weicocogoat/FYP_Integrate_MRAM-FPGA/FYP_Report/Chapter 4/ip-cores-communication_controller_i2c_slave/rtl/i2cSlave.v

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
`include "i2cSlave_define.v"


module i2cSlave (
  clk,
  rst,
  sda,
  scl,
  myReg0,
  myReg1,
  myReg2,
  myReg3,
  data_lb,
  data_ub,
  myReg6,
  myReg7,
  myReg8,
  myReg9,
  myReg10,
  myReg11,
  myReg12,
  myReg13,
  myReg14,
  myReg15,
  chip_en,
  read_en,
  write_en,
  lb_en,
  ub_en
);

input clk;
input rst;
inout sda;
input scl;
output [7:0] myReg0;
output [7:0] myReg1;
output [7:0] myReg2;
output [7:0] myReg3;
inout [7:0] data_lb;
inout [7:0] data_ub;
output [7:0] myReg6;
output [7:0] myReg7;
input [7:0] myReg8;
input [7:0] myReg9;
input [7:0] myReg10;
input [7:0] myReg11;
input [7:0] myReg12;
input [7:0] myReg13;
input [7:0] myReg14;
input [7:0] myReg15;
output chip_en;
output read_en;
output write_en;
output lb_en;
output ub_en;


// local wires and regs
reg sdaDeb;
reg sclDeb;
reg [`DEB_I2C_LEN-1:0] sdaPipe;
reg [`DEB_I2C_LEN-1:0] sclPipe;

reg [`SCL_DEL_LEN-1:0] sclDelayed;
reg [`SDA_DEL_LEN-1:0] sdaDelayed;
reg [1:0] startStopDetState;
wire clearStartStopDet;
wire sdaOut;
wire sdaIn;
wire [7:0] regAddr;
wire [7:0] dataToRegIF;
wire writeEn;
wire [7:0] dataFromRegIF;
reg [1:0] rstPipe;
wire rstSyncToClk;
reg startEdgeDet;

assign sda = (sdaOut == 1'b0) ? 1'b0 : 1'bz;
assign sdaIn = sda;

// sync rst rsing edge to clk
always @(posedge clk) begin
  if (rst == 1'b1)
    rstPipe <= 2'b11;
  else
    rstPipe <= {rstPipe[0], 1'b0};
end

assign rstSyncToClk = rstPipe[1];

// debounce sda and scl
always @(posedge clk) begin
  if (rstSyncToClk == 1'b1) begin
    sdaPipe <= {`DEB_I2C_LEN{1'b1}};
    sdaDeb <= 1'b1;
    sclPipe <= {`DEB_I2C_LEN{1'b1}};
    sclDeb <= 1'b1;
  end
  else begin
    sdaPipe <= {sdaPipe[`DEB_I2C_LEN-2:0], sdaIn};
    sclPipe <= {sclPipe[`DEB_I2C_LEN-2:0], scl};
    if (&sclPipe[`DEB_I2C_LEN-1:1] == 1'b1)
      sclDeb <= 1'b1;
    else if (|sclPipe[`DEB_I2C_LEN-1:1] == 1'b0)
      sclDeb <= 1'b0;
    if (&sdaPipe[`DEB_I2C_LEN-1:1] == 1'b1)
      sdaDeb <= 1'b1;
    else if (|sdaPipe[`DEB_I2C_LEN-1:1] == 1'b0)
      sdaDeb <= 1'b0;
  end
end


// delay scl and sda
// sclDelayed is used as a delayed sampling clock
// sdaDelayed is only used for start stop detection
// Because sda hold time from scl falling is 0nS
// sda must be delayed with respect to scl to avoid incorrect
// detection of start/stop at scl falling edge. 
always @(posedge clk) begin
  if (rstSyncToClk == 1'b1) begin
    sclDelayed <= {`SCL_DEL_LEN{1'b1}};
    sdaDelayed <= {`SDA_DEL_LEN{1'b1}};
  end
  else begin
    sclDelayed <= {sclDelayed[`SCL_DEL_LEN-2:0], sclDeb};
    sdaDelayed <= {sdaDelayed[`SDA_DEL_LEN-2:0], sdaDeb};
  end
end

// start stop detection
always @(posedge clk) begin
  if (rstSyncToClk == 1'b1) begin
    startStopDetState <= `NULL_DET;
    startEdgeDet <= 1'b0;
  end
  else begin
    if (sclDeb == 1'b1 && sdaDelayed[`SDA_DEL_LEN-2] == 1'b0 && sdaDelayed[`SDA_DEL_LEN-1] == 1'b1)
      startEdgeDet <= 1'b1;
    else
      startEdgeDet <= 1'b0;
    if (clearStartStopDet == 1'b1)
      startStopDetState <= `NULL_DET;
    else if (sclDeb == 1'b1) begin
      if (sdaDelayed[`SDA_DEL_LEN-2] == 1'b1 && sdaDelayed[`SDA_DEL_LEN-1] == 1'b0) 
        startStopDetState <= `STOP_DET;
      else if (sdaDelayed[`SDA_DEL_LEN-2] == 1'b0 && sdaDelayed[`SDA_DEL_LEN-1] == 1'b1)
        startStopDetState <= `START_DET;
    end
  end
end


registerInterface u_registerInterface(
  .clk(clk),
  .addr(regAddr),
  .dataIn(dataToRegIF),
  .writeEn(writeEn),
  .dataOut(dataFromRegIF),
  .myReg0(myReg0),
  .myReg1(myReg1),
  .myReg2(myReg2),
  .myReg3(myReg3),
  .data_lb(data_lb),
  .data_ub(data_ub),
  .myReg6(myReg6),
  .myReg7(myReg7),
  .myReg8(myReg8),
  .myReg9(myReg9),
  .myReg10(myReg10),
  .myReg11(myReg11),
  .myReg12(myReg12),
  .myReg13(myReg13),
  .myReg14(myReg14),
  .myReg15(myReg15),
  .chip_en(chip_en),
  .read_en(read_en),
  .write_en(write_en),
  .lb_en(lb_en),
  .ub_en(ub_en)
);

serialInterface u_serialInterface (
  .clk(clk), 
  .rst(rstSyncToClk | startEdgeDet), 
  .dataIn(dataFromRegIF), 
  .dataOut(dataToRegIF), 
  .writeEn(writeEn),
  .regAddr(regAddr), 
  .scl(sclDelayed[`SCL_DEL_LEN-1]), 
  .sdaIn(sdaDeb), 
  .sdaOut(sdaOut), 
  .startStopDetState(startStopDetState),
  .clearStartStopDet(clearStartStopDet) 
);


endmodule
