weicocogoat/FYP_Integrate_MRAM-FPGA/SPS Burst/design_1_wrapper.v

//Copyright 1986-2022 Xilinx, Inc. All Rights Reserved.
//Copyright 2022-2024 Advanced Micro Devices, Inc. All Rights Reserved.
//--------------------------------------------------------------------------------
//Tool Version: Vivado v.2024.1.1 (win64) Build 5094488 Fri Jun 14 08:59:21 MDT 2024
//Date        : Thu Dec 26 22:09:19 2024
//Host        : LAPTOP-NHK267EJ running 64-bit major release  (build 9200)
//Command     : generate_target design_1_wrapper.bd
//Design      : design_1_wrapper
//Purpose     : IP block netlist
//--------------------------------------------------------------------------------
`timescale 1 ps / 1 ps

module design_1_wrapper
   (DDR_addr,
    DDR_ba,
    DDR_cas_n,
    DDR_ck_n,
    DDR_ck_p,
    DDR_cke,
    DDR_cs_n,
    DDR_dm,
    DDR_dq,
    DDR_dqs_n,
    DDR_dqs_p,
    DDR_odt,
    DDR_ras_n,
    DDR_reset_n,
    DDR_we_n,
    FIXED_IO_ddr_vrn,
    FIXED_IO_ddr_vrp,
    FIXED_IO_mio,
    FIXED_IO_ps_clk,
    FIXED_IO_ps_porb,
    FIXED_IO_ps_srstb,
    gpio_rtl_0_tri_io,
    gpio_rtl_tri_io);
  inout [14:0]DDR_addr;
  inout [2:0]DDR_ba;
  inout DDR_cas_n;
  inout DDR_ck_n;
  inout DDR_ck_p;
  inout DDR_cke;
  inout DDR_cs_n;
  inout [3:0]DDR_dm;
  inout [31:0]DDR_dq;
  inout [3:0]DDR_dqs_n;
  inout [3:0]DDR_dqs_p;
  inout DDR_odt;
  inout DDR_ras_n;
  inout DDR_reset_n;
  inout DDR_we_n;
  inout FIXED_IO_ddr_vrn;
  inout FIXED_IO_ddr_vrp;
  inout [53:0]FIXED_IO_mio;
  inout FIXED_IO_ps_clk;
  inout FIXED_IO_ps_porb;
  inout FIXED_IO_ps_srstb;
  inout [0:0]gpio_rtl_0_tri_io;
  inout [9:0]gpio_rtl_tri_io;

  wire [14:0]DDR_addr;
  wire [2:0]DDR_ba;
  wire DDR_cas_n;
  wire DDR_ck_n;
  wire DDR_ck_p;
  wire DDR_cke;
  wire DDR_cs_n;
  wire [3:0]DDR_dm;
  wire [31:0]DDR_dq;
  wire [3:0]DDR_dqs_n;
  wire [3:0]DDR_dqs_p;
  wire DDR_odt;
  wire DDR_ras_n;
  wire DDR_reset_n;
  wire DDR_we_n;
  wire FIXED_IO_ddr_vrn;
  wire FIXED_IO_ddr_vrp;
  wire [53:0]FIXED_IO_mio;
  wire FIXED_IO_ps_clk;
  wire FIXED_IO_ps_porb;
  wire FIXED_IO_ps_srstb;
  wire [0:0]gpio_rtl_0_tri_i_0;
  wire [0:0]gpio_rtl_0_tri_io_0;
  wire [0:0]gpio_rtl_0_tri_o_0;
  wire [0:0]gpio_rtl_0_tri_t_0;
  wire [0:0]gpio_rtl_tri_i_0;
  wire [1:1]gpio_rtl_tri_i_1;
  wire [2:2]gpio_rtl_tri_i_2;
  wire [3:3]gpio_rtl_tri_i_3;
  wire [4:4]gpio_rtl_tri_i_4;
  wire [5:5]gpio_rtl_tri_i_5;
  wire [6:6]gpio_rtl_tri_i_6;
  wire [7:7]gpio_rtl_tri_i_7;
  wire [8:8]gpio_rtl_tri_i_8;
  wire [9:9]gpio_rtl_tri_i_9;
  wire [0:0]gpio_rtl_tri_io_0;
  wire [1:1]gpio_rtl_tri_io_1;
  wire [2:2]gpio_rtl_tri_io_2;
  wire [3:3]gpio_rtl_tri_io_3;
  wire [4:4]gpio_rtl_tri_io_4;
  wire [5:5]gpio_rtl_tri_io_5;
  wire [6:6]gpio_rtl_tri_io_6;
  wire [7:7]gpio_rtl_tri_io_7;
  wire [8:8]gpio_rtl_tri_io_8;
  wire [9:9]gpio_rtl_tri_io_9;
  wire [0:0]gpio_rtl_tri_o_0;
  wire [1:1]gpio_rtl_tri_o_1;
  wire [2:2]gpio_rtl_tri_o_2;
  wire [3:3]gpio_rtl_tri_o_3;
  wire [4:4]gpio_rtl_tri_o_4;
  wire [5:5]gpio_rtl_tri_o_5;
  wire [6:6]gpio_rtl_tri_o_6;
  wire [7:7]gpio_rtl_tri_o_7;
  wire [8:8]gpio_rtl_tri_o_8;
  wire [9:9]gpio_rtl_tri_o_9;
  wire [0:0]gpio_rtl_tri_t_0;
  wire [1:1]gpio_rtl_tri_t_1;
  wire [2:2]gpio_rtl_tri_t_2;
  wire [3:3]gpio_rtl_tri_t_3;
  wire [4:4]gpio_rtl_tri_t_4;
  wire [5:5]gpio_rtl_tri_t_5;
  wire [6:6]gpio_rtl_tri_t_6;
  wire [7:7]gpio_rtl_tri_t_7;
  wire [8:8]gpio_rtl_tri_t_8;
  wire [9:9]gpio_rtl_tri_t_9;

  design_1 design_1_i
       (.DDR_addr(DDR_addr),
        .DDR_ba(DDR_ba),
        .DDR_cas_n(DDR_cas_n),
        .DDR_ck_n(DDR_ck_n),
        .DDR_ck_p(DDR_ck_p),
        .DDR_cke(DDR_cke),
        .DDR_cs_n(DDR_cs_n),
        .DDR_dm(DDR_dm),
        .DDR_dq(DDR_dq),
        .DDR_dqs_n(DDR_dqs_n),
        .DDR_dqs_p(DDR_dqs_p),
        .DDR_odt(DDR_odt),
        .DDR_ras_n(DDR_ras_n),
        .DDR_reset_n(DDR_reset_n),
        .DDR_we_n(DDR_we_n),
        .FIXED_IO_ddr_vrn(FIXED_IO_ddr_vrn),
        .FIXED_IO_ddr_vrp(FIXED_IO_ddr_vrp),
        .FIXED_IO_mio(FIXED_IO_mio),
        .FIXED_IO_ps_clk(FIXED_IO_ps_clk),
        .FIXED_IO_ps_porb(FIXED_IO_ps_porb),
        .FIXED_IO_ps_srstb(FIXED_IO_ps_srstb),
        .gpio_rtl_0_tri_i(gpio_rtl_0_tri_i_0),
        .gpio_rtl_0_tri_o(gpio_rtl_0_tri_o_0),
        .gpio_rtl_0_tri_t(gpio_rtl_0_tri_t_0),
        .gpio_rtl_tri_i({gpio_rtl_tri_i_9,gpio_rtl_tri_i_8,gpio_rtl_tri_i_7,gpio_rtl_tri_i_6,gpio_rtl_tri_i_5,gpio_rtl_tri_i_4,gpio_rtl_tri_i_3,gpio_rtl_tri_i_2,gpio_rtl_tri_i_1,gpio_rtl_tri_i_0}),
        .gpio_rtl_tri_o({gpio_rtl_tri_o_9,gpio_rtl_tri_o_8,gpio_rtl_tri_o_7,gpio_rtl_tri_o_6,gpio_rtl_tri_o_5,gpio_rtl_tri_o_4,gpio_rtl_tri_o_3,gpio_rtl_tri_o_2,gpio_rtl_tri_o_1,gpio_rtl_tri_o_0}),
        .gpio_rtl_tri_t({gpio_rtl_tri_t_9,gpio_rtl_tri_t_8,gpio_rtl_tri_t_7,gpio_rtl_tri_t_6,gpio_rtl_tri_t_5,gpio_rtl_tri_t_4,gpio_rtl_tri_t_3,gpio_rtl_tri_t_2,gpio_rtl_tri_t_1,gpio_rtl_tri_t_0}));
  IOBUF gpio_rtl_0_tri_iobuf_0
       (.I(gpio_rtl_0_tri_o_0),
        .IO(gpio_rtl_0_tri_io[0]),
        .O(gpio_rtl_0_tri_i_0),
        .T(gpio_rtl_0_tri_t_0));
  IOBUF gpio_rtl_tri_iobuf_0
       (.I(gpio_rtl_tri_o_0),
        .IO(gpio_rtl_tri_io[0]),
        .O(gpio_rtl_tri_i_0),
        .T(gpio_rtl_tri_t_0));
  IOBUF gpio_rtl_tri_iobuf_1
       (.I(gpio_rtl_tri_o_1),
        .IO(gpio_rtl_tri_io[1]),
        .O(gpio_rtl_tri_i_1),
        .T(gpio_rtl_tri_t_1));
  IOBUF gpio_rtl_tri_iobuf_2
       (.I(gpio_rtl_tri_o_2),
        .IO(gpio_rtl_tri_io[2]),
        .O(gpio_rtl_tri_i_2),
        .T(gpio_rtl_tri_t_2));
  IOBUF gpio_rtl_tri_iobuf_3
       (.I(gpio_rtl_tri_o_3),
        .IO(gpio_rtl_tri_io[3]),
        .O(gpio_rtl_tri_i_3),
        .T(gpio_rtl_tri_t_3));
  IOBUF gpio_rtl_tri_iobuf_4
       (.I(gpio_rtl_tri_o_4),
        .IO(gpio_rtl_tri_io[4]),
        .O(gpio_rtl_tri_i_4),
        .T(gpio_rtl_tri_t_4));
  IOBUF gpio_rtl_tri_iobuf_5
       (.I(gpio_rtl_tri_o_5),
        .IO(gpio_rtl_tri_io[5]),
        .O(gpio_rtl_tri_i_5),
        .T(gpio_rtl_tri_t_5));
  IOBUF gpio_rtl_tri_iobuf_6
       (.I(gpio_rtl_tri_o_6),
        .IO(gpio_rtl_tri_io[6]),
        .O(gpio_rtl_tri_i_6),
        .T(gpio_rtl_tri_t_6));
  IOBUF gpio_rtl_tri_iobuf_7
       (.I(gpio_rtl_tri_o_7),
        .IO(gpio_rtl_tri_io[7]),
        .O(gpio_rtl_tri_i_7),
        .T(gpio_rtl_tri_t_7));
  IOBUF gpio_rtl_tri_iobuf_8
       (.I(gpio_rtl_tri_o_8),
        .IO(gpio_rtl_tri_io[8]),
        .O(gpio_rtl_tri_i_8),
        .T(gpio_rtl_tri_t_8));
  IOBUF gpio_rtl_tri_iobuf_9
       (.I(gpio_rtl_tri_o_9),
        .IO(gpio_rtl_tri_io[9]),
        .O(gpio_rtl_tri_i_9),
        .T(gpio_rtl_tri_t_9));
endmodule
