weicocogoat/FYP_Integrate_MRAM-FPGA/Zedboard_FMC_Testing/LED&DIP_constraints.xdc

# Zedboard on-board DIP switches and LED constraints file

# DIP Switches
set_property PACKAGE_PIN F22 [get_ports {gpio_rtl_tri_io[0]}] 
set_property PACKAGE_PIN G22 [get_ports {gpio_rtl_tri_io[1]}] 
set_property PACKAGE_PIN H22 [get_ports {gpio_rtl_tri_io[2]}] 
set_property PACKAGE_PIN F21 [get_ports {gpio_rtl_tri_io[3]}] 
set_property PACKAGE_PIN H19 [get_ports {gpio_rtl_tri_io[4]}] 
set_property PACKAGE_PIN H18 [get_ports {gpio_rtl_tri_io[5]}] 
set_property PACKAGE_PIN H17 [get_ports {gpio_rtl_tri_io[6]}] 
set_property PACKAGE_PIN M15 [get_ports {gpio_rtl_tri_io[7]}] 

# LED
set_property PACKAGE_PIN T22 [get_ports {gpio_rtl_0_tri_io[0]}] 
set_property PACKAGE_PIN T21 [get_ports {gpio_rtl_0_tri_io[1]}] 
set_property PACKAGE_PIN U22 [get_ports {gpio_rtl_0_tri_io[2]}] 
set_property PACKAGE_PIN U21 [get_ports {gpio_rtl_0_tri_io[3]}] 
set_property PACKAGE_PIN V22 [get_ports {gpio_rtl_0_tri_io[4]}] 
set_property PACKAGE_PIN W22 [get_ports {gpio_rtl_0_tri_io[5]}] 
set_property PACKAGE_PIN U19 [get_ports {gpio_rtl_0_tri_io[6]}] 
set_property PACKAGE_PIN U14 [get_ports {gpio_rtl_0_tri_io[7]}] 
set_property PACKAGE_PIN U14 [get_ports {gpio_rtl_0_tri_io[7]}] 

# 3.3v
set_property IOSTANDARD LVCMOS33 [get_ports {gpio_rtl_tri_io[*]}] 
set_property IOSTANDARD LVCMOS33 [get_ports {gpio_rtl_0_tri_io[*]}] 

set_property PULLDOWN true [get_ports {gpio_rtl_tri_io[*]}] 
set_property PULLDOWN true [get_ports {gpio_rtl_0_tri_io[*]}] 
