weicocogoat/FYP_Integrate_MRAM-FPGA/FYP_Report/Chapter 5/Section 5.2/Pi Pico/Blinking LED/blink.py

from machine import Pin, Timer

led = Pin(10, Pin.OUT)
LED_state = True
tim = Timer()

def tick(timer):
    global led, LED_state
    LED_state = not LED_state
    led.value(LED_state)

tim.init(freq=1, mode = Timer.PERIODIC, callback=tick)
